xstreamworship/compact-eurocard/diagrams-pictures/3ru-cec-card.png

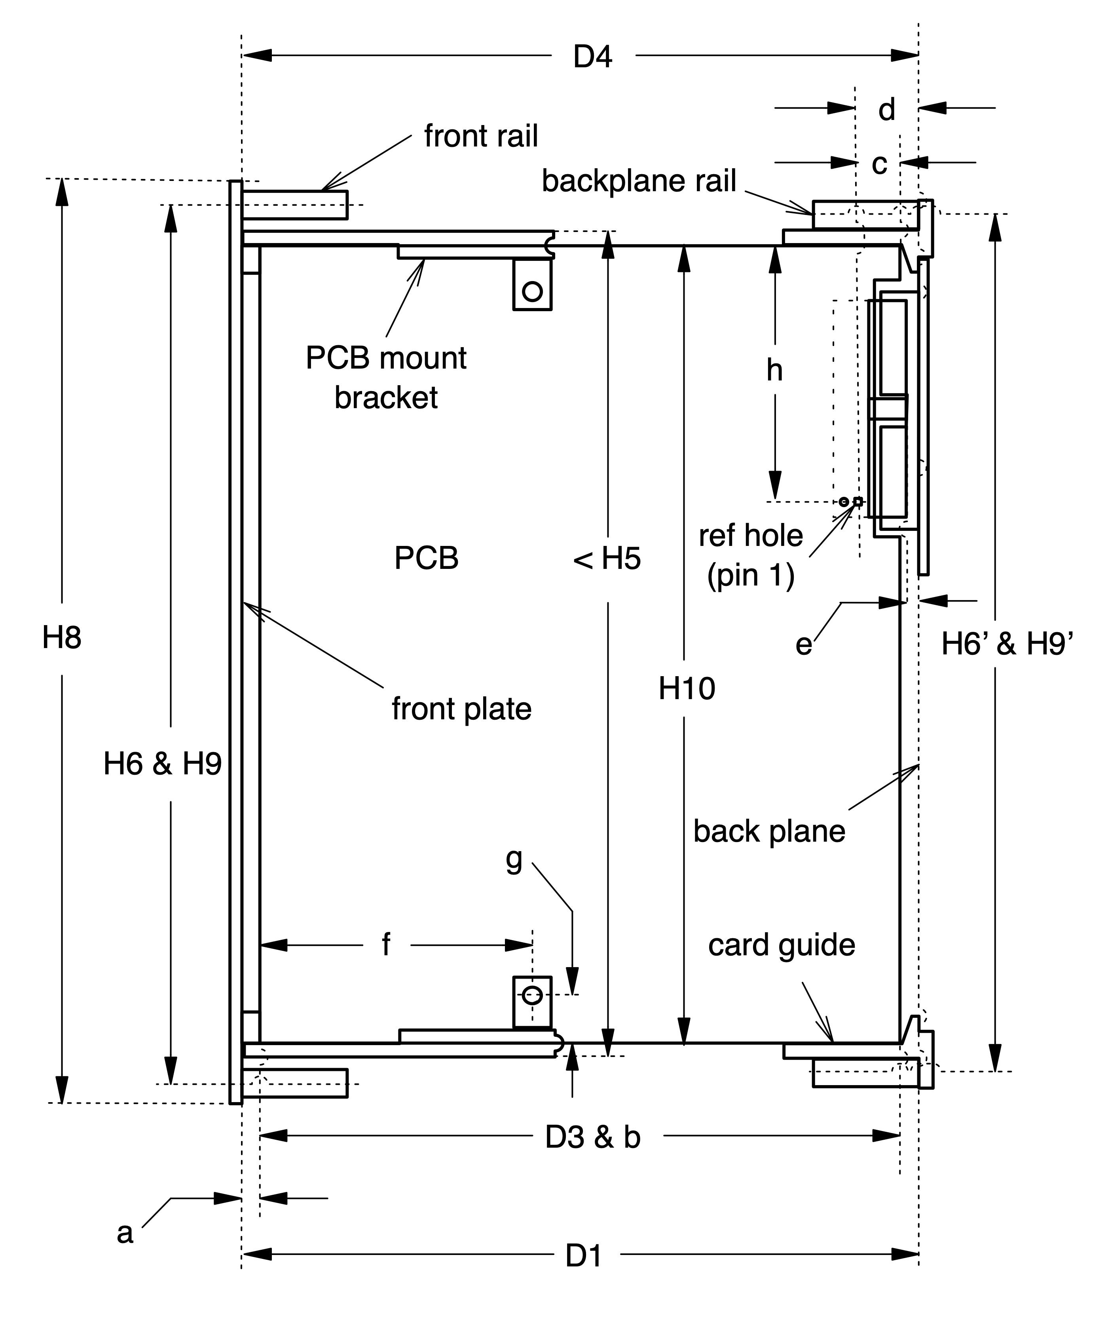
diagrams-pictures/3ru-cec-card.png
