xstreamworship/compact-eurocard/diagrams-pictures/3ru-panel.png

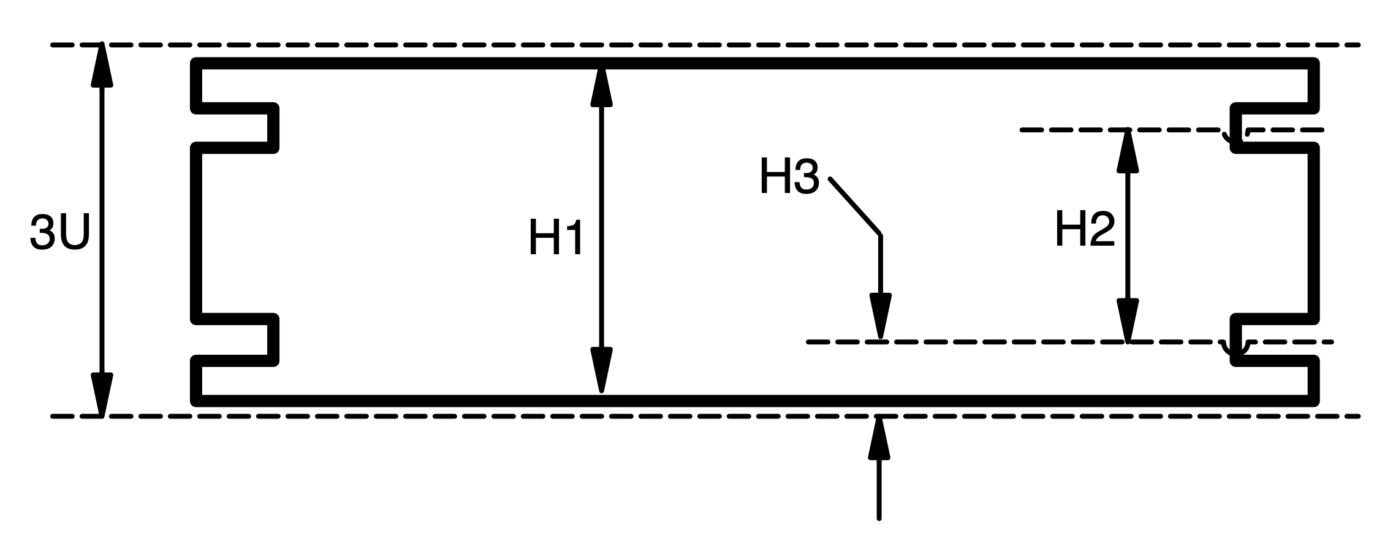
diagrams-pictures/3ru-panel.png
