xstreamworship/compact-eurocard/diagrams-pictures/cards-in-cage-with-eurorack-module-1.jpeg

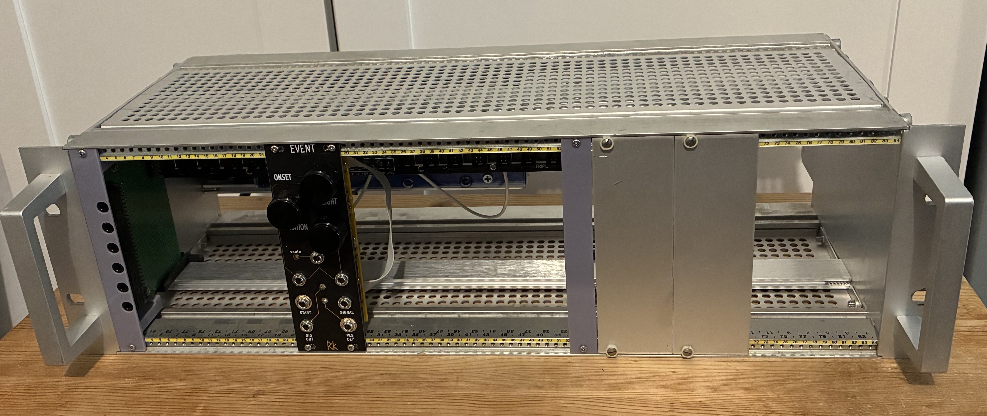
diagrams-pictures/cards-in-cage-with-eurorack-module-1.jpeg
