xstreamworship/compact-eurocard/diagrams-pictures/cards-in-cage-with-eurotack-module-2.jpeg

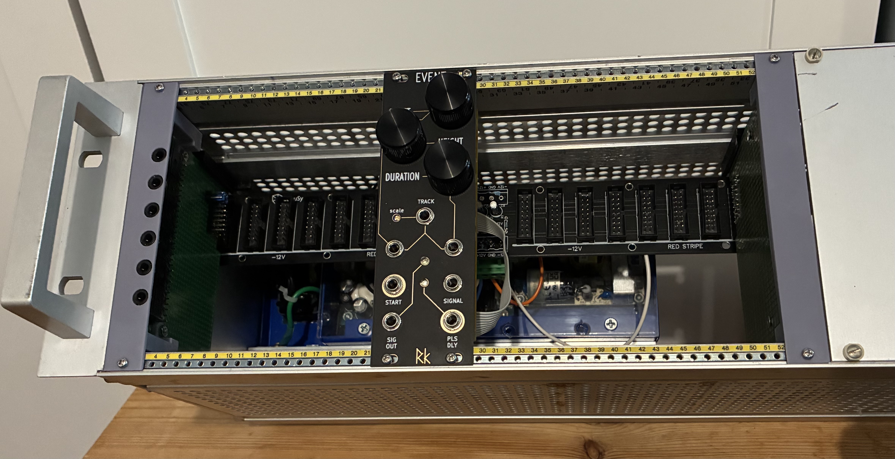
diagrams-pictures/cards-in-cage-with-eurotack-module-2.jpeg
