xstreamworship/compact-eurocard/diagrams-pictures/front-view-6jackholes.jpeg

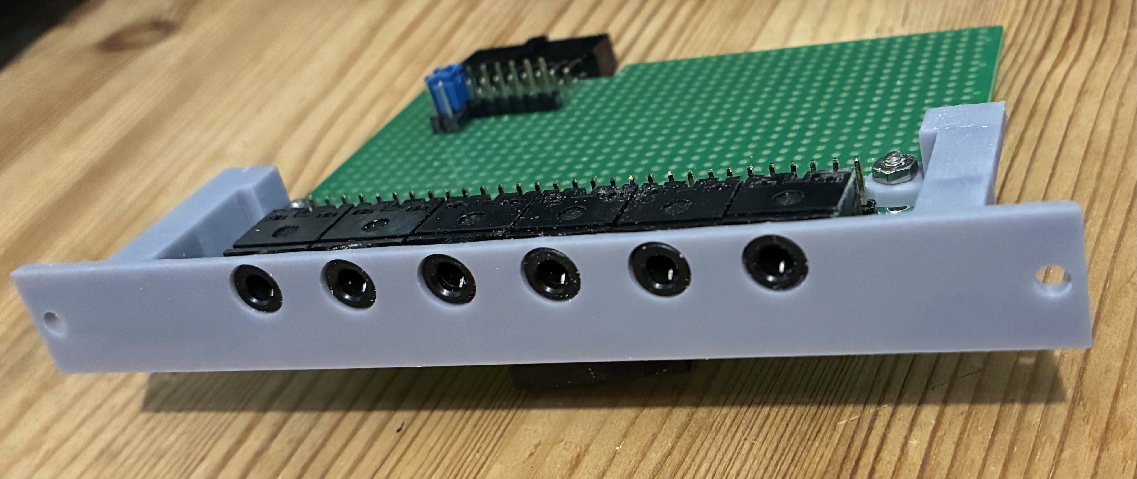
diagrams-pictures/front-view-6jackholes.jpeg
