xstreamworship/compact-eurocard/diagrams-pictures/front-view-into-cage-1.jpeg

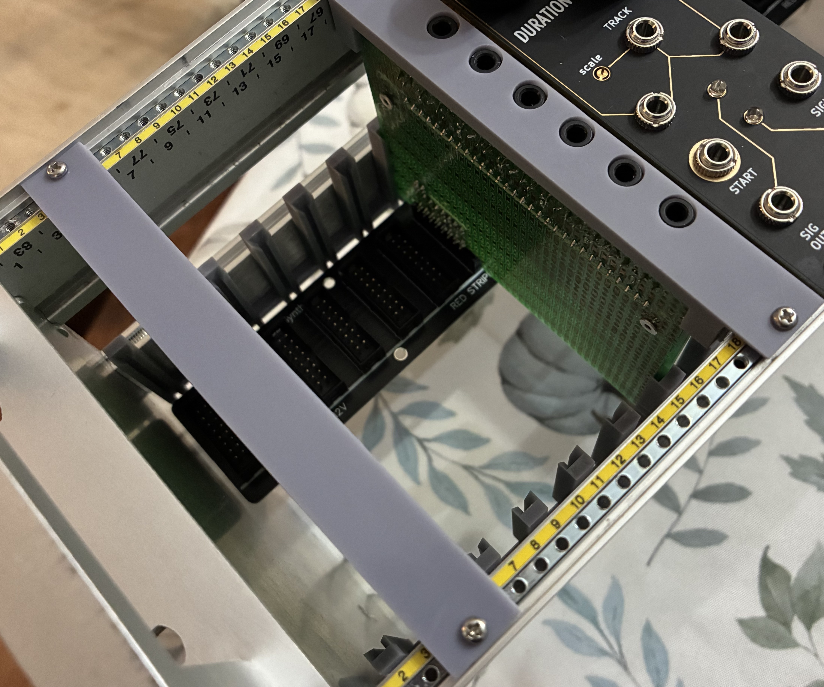
diagrams-pictures/front-view-into-cage-1.jpeg
