xstreamworship/compact-eurocard/diagrams-pictures/front-view-into-cage-2.jpeg

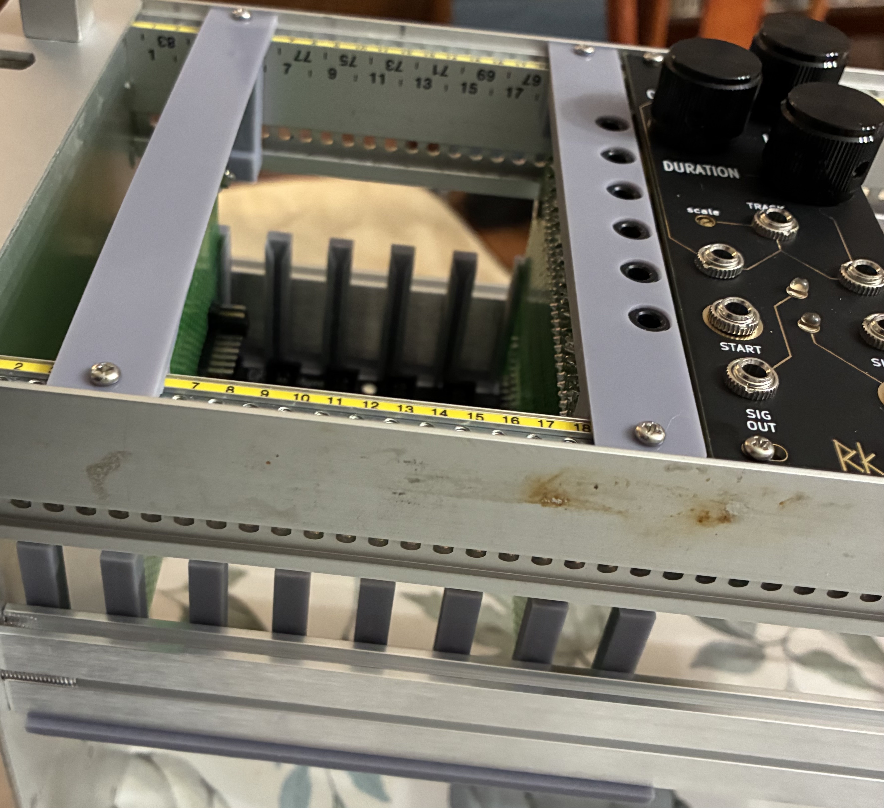
diagrams-pictures/front-view-into-cage-2.jpeg
