xstreamworship/compact-eurocard/diagrams-pictures/front-view-into-cage-4.jpeg

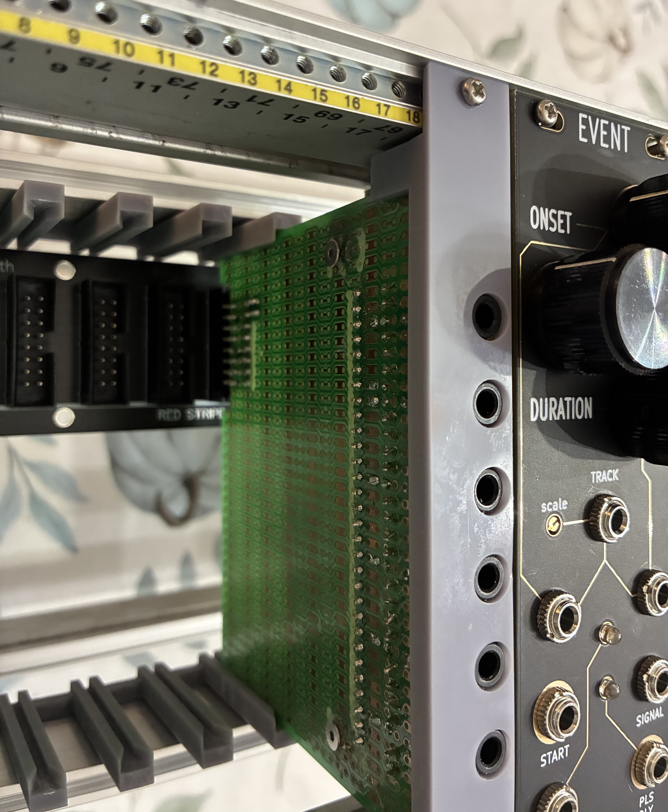
diagrams-pictures/front-view-into-cage-4.jpeg
