xstreamworship/compact-eurocard/diagrams-pictures/top-edge-bracket-detail.jpeg

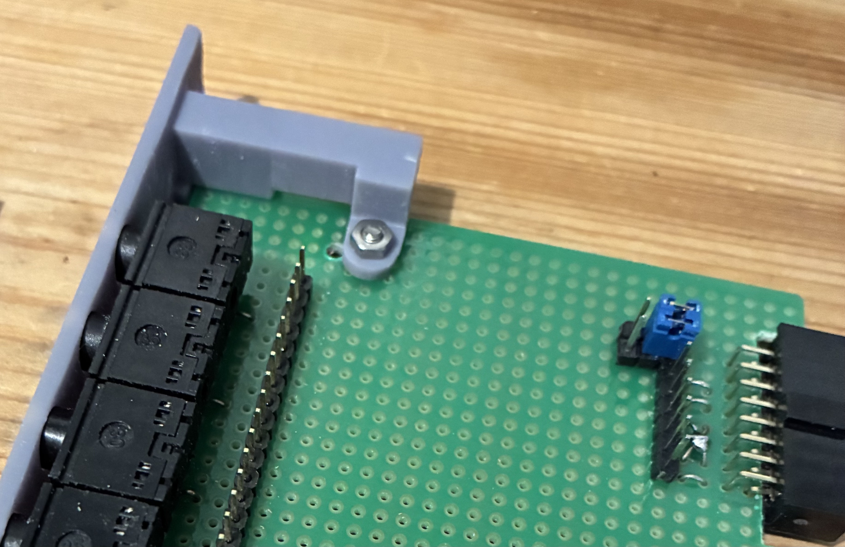
diagrams-pictures/top-edge-bracket-detail.jpeg
