xstreamworship/compact-eurocard/diagrams-pictures/top-view-bracket-1.jpeg

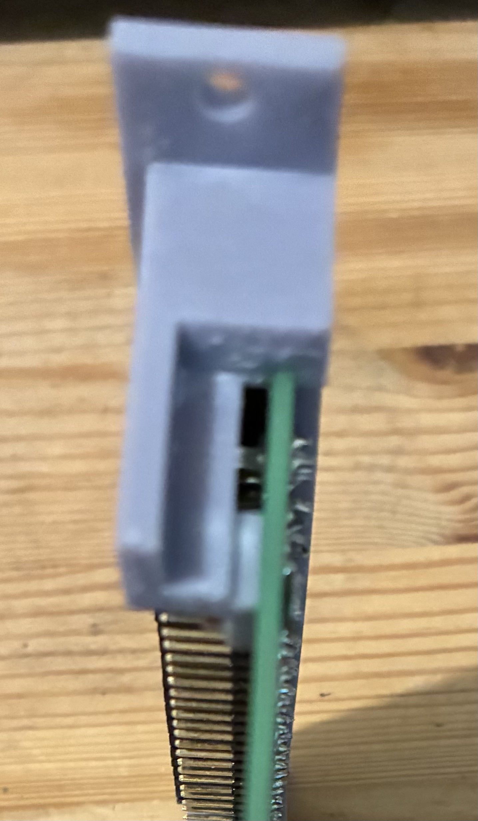
diagrams-pictures/top-view-bracket-1.jpeg
