xstreamworship/compact-eurocard/diagrams-pictures/top-view-bracket-2.jpeg

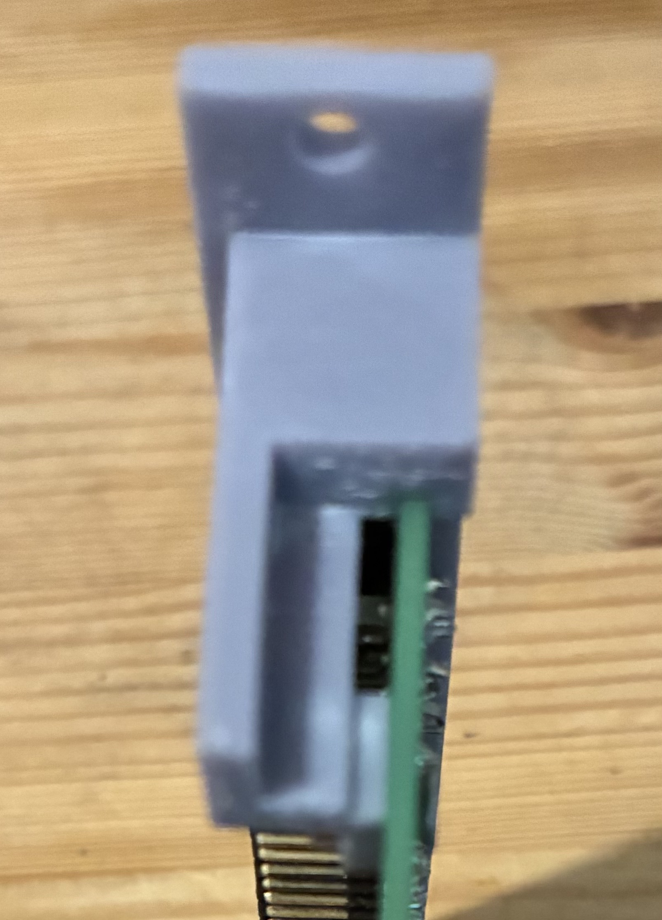
diagrams-pictures/top-view-bracket-2.jpeg
