xstreamworship/compact-eurocard/diagrams-pictures/rear-view-cardguides-1.jpeg

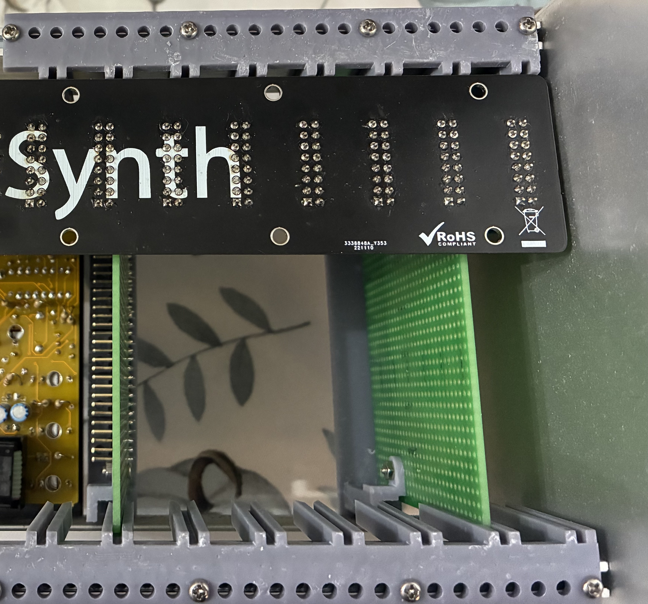
diagrams-pictures/rear-view-cardguides-1.jpeg
