xstreamworship/compact-eurocard/diagrams-pictures/rear-view-cards-in-cardguide-1.jpeg

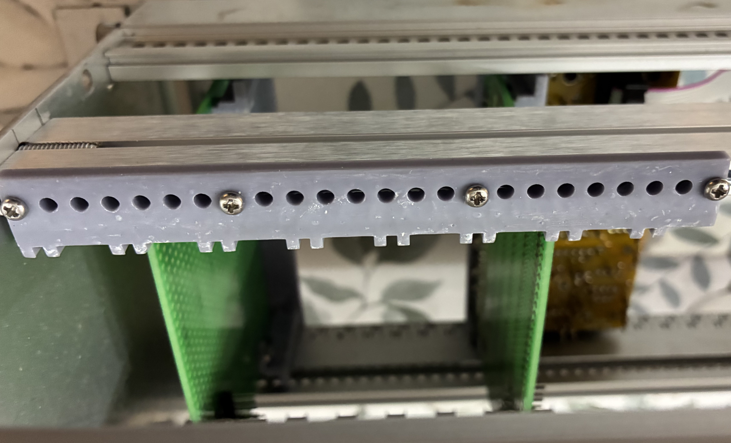
diagrams-pictures/rear-view-cards-in-cardguide-1.jpeg
