xstreamworship/compact-eurocard/diagrams-pictures/showing-clearance-of-cardguide-1.jpeg

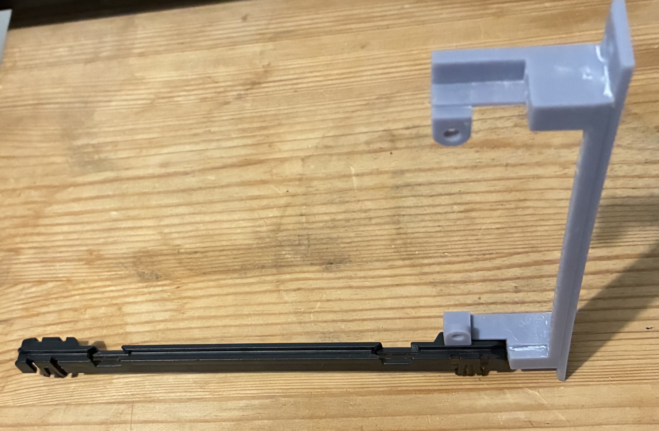
diagrams-pictures/showing-clearance-of-cardguide-1.jpeg
