xstreamworship/compact-eurocard/diagrams-pictures/showing-clearance-of-cardguide-2.jpeg

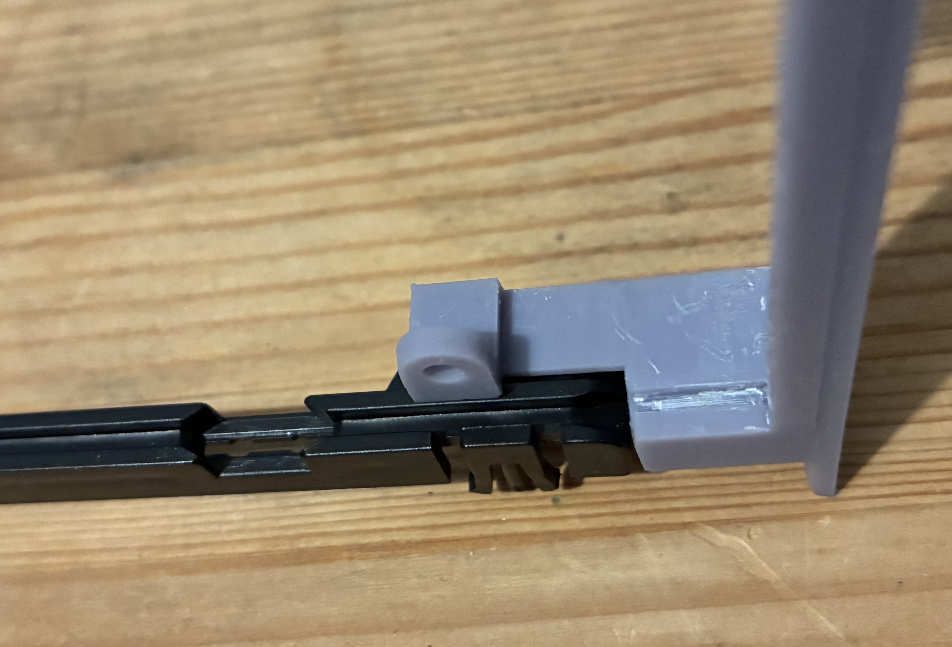
diagrams-pictures/showing-clearance-of-cardguide-2.jpeg
