xstreamworship/compact-eurocard/diagrams-pictures/top-angle-view-cardguides-1.jpeg

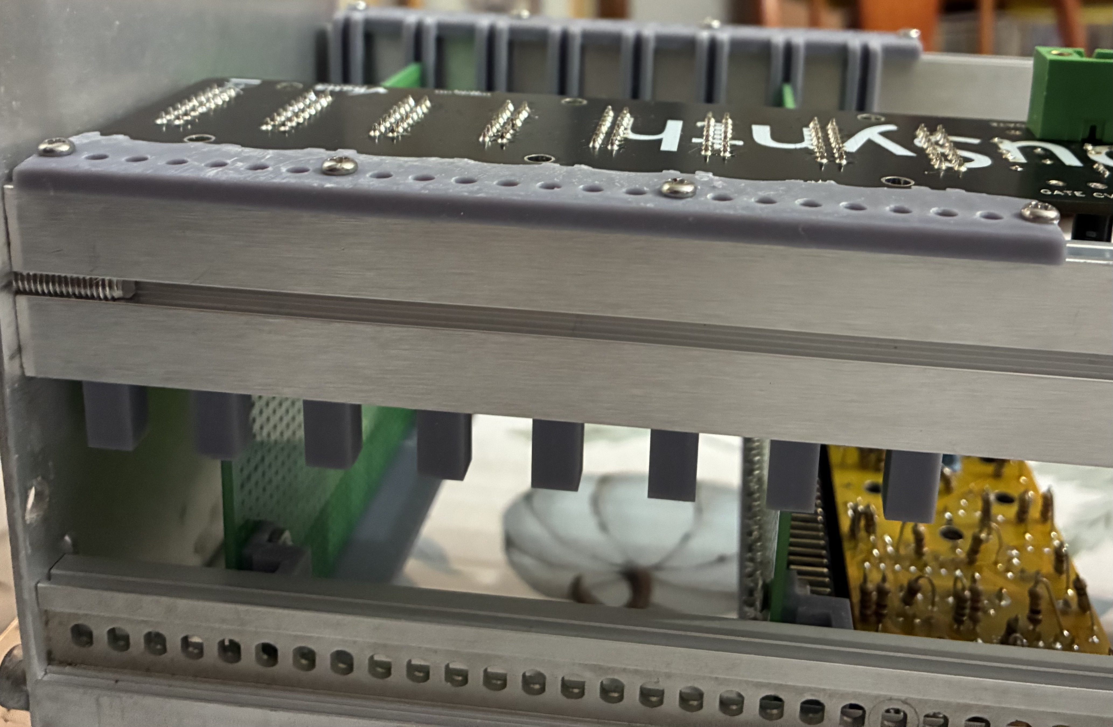
diagrams-pictures/top-angle-view-cardguides-1.jpeg
